peekpt/MicroSolderingStation/src/bitmap_logo.h

#ifndef bitmap_logo_h
#define bitmap_logo_h

#define BITMAP_LOGO_WIDTH  84
#define BITMAP_LOGO_HEIGHT 48

const unsigned char bitmap_logo[] PROGMEM = 
{
   0x00, 0x00, 0x00, 0x00, 0x00, 0x00, 0x00, 0x00, 0x00, 0x00, 0x00, 0x7e,
   0x7e, 0x02, 0x6e, 0xdc, 0xb9, 0x93, 0x20, 0x3f, 0x00, 0x00, 0x42, 0x42,
   0x02, 0x82, 0x04, 0x08, 0x92, 0x21, 0x31, 0x00, 0x00, 0x16, 0x42, 0x02,
   0x82, 0x4c, 0x18, 0x92, 0x2a, 0x01, 0x00, 0x00, 0x68, 0x42, 0x02, 0x82,
   0xdc, 0xb8, 0x91, 0x2a, 0x39, 0x00, 0x00, 0x42, 0x42, 0x02, 0x82, 0x04,
   0x08, 0x92, 0x30, 0x21, 0x00, 0x00, 0x7e, 0x7e, 0xee, 0x6e, 0xdc, 0x09,
   0x92, 0x20, 0x3f, 0x00, 0x00, 0x00, 0x00, 0x00, 0x00, 0x00, 0x00, 0x00,
   0x00, 0x00, 0x00, 0x00, 0x00, 0x00, 0xfc, 0x1f, 0x00, 0x00, 0x00, 0x00,
   0x00, 0x00, 0x00, 0x00, 0x00, 0x3e, 0x20, 0x00, 0x00, 0x00, 0x00, 0x00,
   0x00, 0x00, 0x00, 0x00, 0x0f, 0x40, 0x7e, 0x7f, 0xbf, 0xbf, 0xfc, 0x08,
   0x02, 0x00, 0x80, 0x07, 0x40, 0x42, 0x08, 0x21, 0x84, 0x84, 0x18, 0x02,
   0x00, 0xc0, 0x07, 0x80, 0x16, 0x08, 0x33, 0x84, 0x84, 0xa8, 0x02, 0x00,
   0xc0, 0x07, 0x80, 0x68, 0x08, 0x3f, 0x84, 0x84, 0xa8, 0x02, 0x00, 0xe0,
   0x07, 0xc0, 0x42, 0x08, 0x21, 0x84, 0x84, 0x08, 0x03, 0x00, 0xe0, 0x07,
   0x40, 0x7e, 0x08, 0x21, 0x84, 0xfc, 0x08, 0x02, 0x00, 0xd0, 0x03, 0x20,
   0x00, 0x00, 0x00, 0x00, 0x00, 0x00, 0x00, 0x00, 0xd0, 0x03, 0x20, 0xff,
   0xff, 0xff, 0xff, 0x3f, 0x00, 0x00, 0x00, 0xe8, 0x03, 0x90, 0xff, 0xff,
   0xff, 0xff, 0x7f, 0x00, 0x00, 0x00, 0xf8, 0x01, 0x88, 0xff, 0xff, 0xff,
   0xff, 0x7f, 0x00, 0x00, 0x00, 0xe8, 0x01, 0x84, 0xff, 0xff, 0xff, 0xff,
   0x7f, 0x00, 0x00, 0x00, 0xec, 0x00, 0x84, 0xff, 0xff, 0xff, 0xff, 0x7f,
   0x00, 0x00, 0x00, 0xe4, 0x00, 0x82, 0x0f, 0x00, 0x00, 0x70, 0x70, 0x00,
   0x00, 0x00, 0xf4, 0x00, 0x81, 0xef, 0x1a, 0x07, 0xb0, 0x6f, 0x00, 0x00,
   0x00, 0x72, 0x80, 0x80, 0xaf, 0x12, 0x07, 0xd0, 0x58, 0x00, 0x00, 0x00,
   0x7a, 0x40, 0x80, 0x0f, 0x00, 0x00, 0x50, 0x50, 0x00, 0x00, 0x00, 0x7b,
   0x20, 0x80, 0xef, 0xbd, 0x87, 0x57, 0x50, 0x00, 0x00, 0x00, 0x39, 0x10,
   0x80, 0x0f, 0xa5, 0x94, 0x57, 0x54, 0x00, 0x00, 0x00, 0x1d, 0x08, 0x80,
   0x0f, 0xa5, 0x04, 0xd0, 0x58, 0x00, 0x00, 0x80, 0x1d, 0x08, 0x80, 0x8f,
   0xa5, 0x84, 0xb7, 0x6f, 0x00, 0x00, 0x80, 0x1e, 0x04, 0x80, 0x0f, 0xa5,
   0xb4, 0x77, 0x70, 0x00, 0x00, 0x80, 0x0e, 0x04, 0x80, 0x0f, 0xa5, 0x14,
   0xf0, 0x7f, 0x00, 0x00, 0x40, 0x0e, 0x02, 0x80, 0xef, 0xbd, 0xb7, 0xf7,
   0x7f, 0x00, 0x00, 0x40, 0x0f, 0x02, 0x80, 0x0f, 0x00, 0x80, 0xf7, 0x7f,
   0x00, 0x00, 0x60, 0x07, 0x01, 0x80, 0xef, 0x0c, 0x00, 0xf0, 0x7f, 0x00,
   0x00, 0xf0, 0x07, 0x01, 0x80, 0xff, 0xff, 0xff, 0xff, 0x7f, 0x00, 0x00,
   0xf0, 0x07, 0x01, 0x80, 0xff, 0xff, 0xff, 0xff, 0x7f, 0x00, 0x00, 0xe0,
   0x03, 0x01, 0x80, 0xff, 0xff, 0xff, 0xff, 0x7f, 0x00, 0x00, 0xc0, 0x03,
   0x01, 0x80, 0xe7, 0xff, 0xff, 0x03, 0x7c, 0x00, 0x00, 0x60, 0x03, 0x02,
   0x80, 0xc3, 0xff, 0xff, 0x3b, 0x7d, 0x00, 0x00, 0x30, 0x00, 0x0c, 0x80,
   0xc3, 0xff, 0xff, 0x3b, 0x7d, 0x00, 0x00, 0x30, 0x00, 0xf0, 0x83, 0xc3,
   0xff, 0xff, 0x3b, 0x7d, 0x00, 0x00, 0x18, 0x00, 0x00, 0xfc, 0xf0, 0xff,
   0xff, 0x03, 0x7c, 0x00, 0x00, 0x18, 0x00, 0x00, 0x00, 0xff, 0xff, 0xff,
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
};



#endif
